rixtox/Topre-to-Cherry-MX-Adapter/STL/Plunger String 2.25x.STL

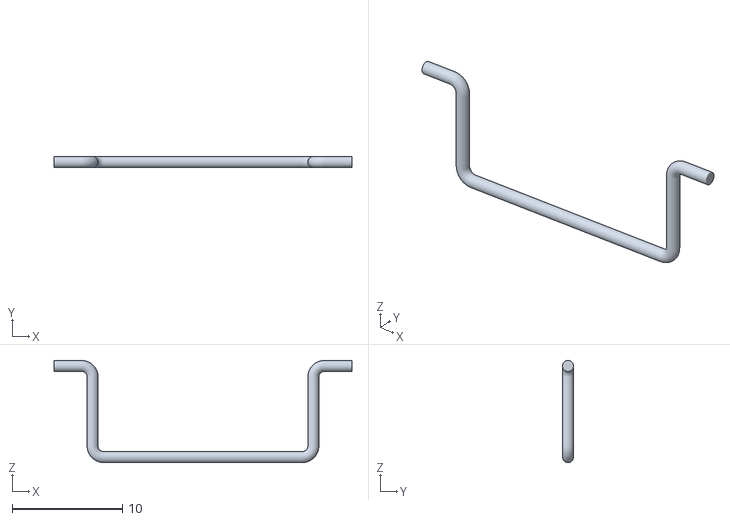
[picture p18: CAD file, 2016-08-14]
STL/Plunger String 2.25x.STL
27.0 x 1.00 x 9.25
