rixtox/Topre-to-Cherry-MX-Adapter/PRT/Stabilizer Plunger Right.SLDPRT

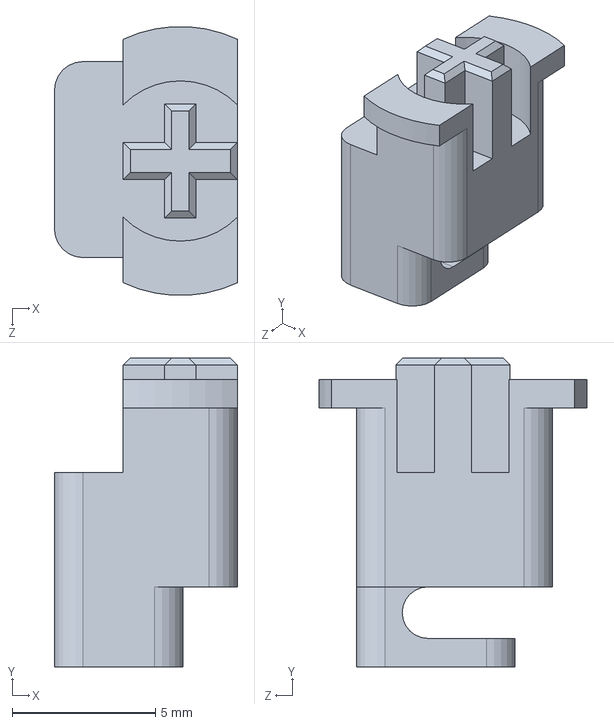
[picture p19: CAD file, 2018-12-25]
PRT/Stabilizer Plunger Right.SLDPRT
6.40 x 10.8 x 9.38 mm
