rixtox/Topre-to-Cherry-MX-Adapter/PRT/Stabilizer Housing Right.SLDPRT

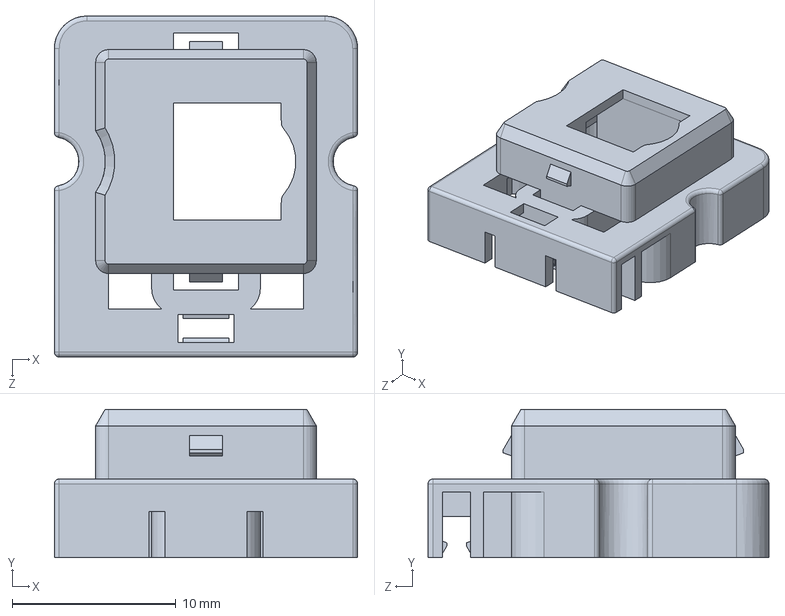
[picture p20: CAD file, 2018-12-25]
PRT/Stabilizer Housing Right.SLDPRT
18.5 x 9.05 x 20.9 mm
